laureatbarbie-eng/CloudCam/raspberry case/Front.STL

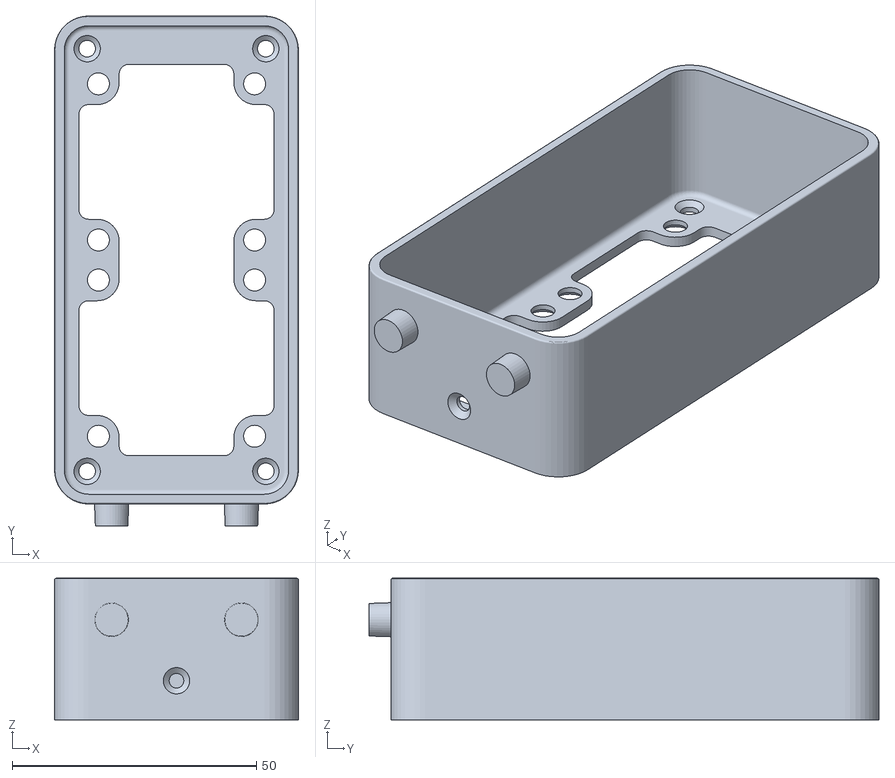
[picture p21: CAD file, 2026-04-14]
raspberry case/Front.STL
50.0 x 104.5 x 29.0
