laureatbarbie-eng/CloudCam/raspberry case/Rear-panel_Pi5-only.STL

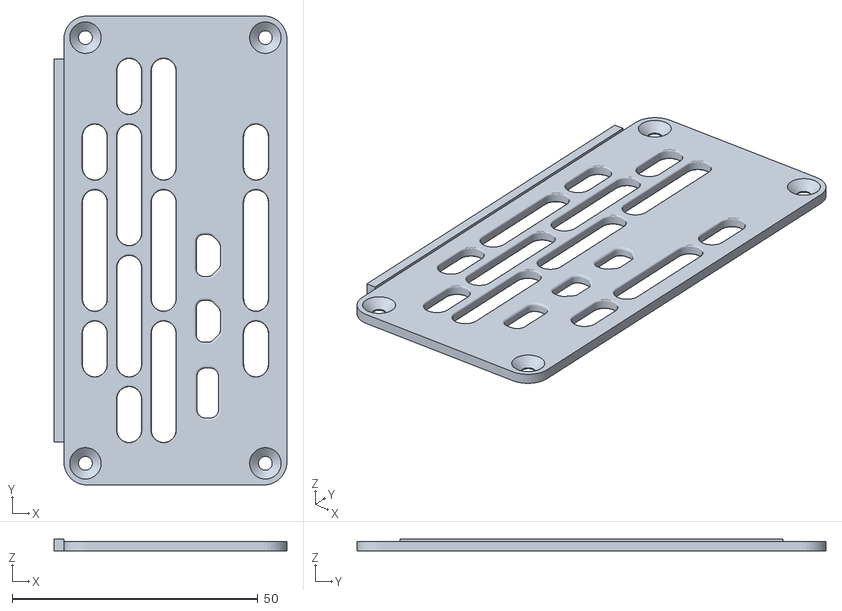
[picture p22: CAD file, 2026-04-14]
raspberry case/Rear-panel_Pi5-only.STL
47.4 x 95.4 x 2.50
